sekt1953/HomeAssistant-NSPanel/First_Try/Nextion/Image/0.png

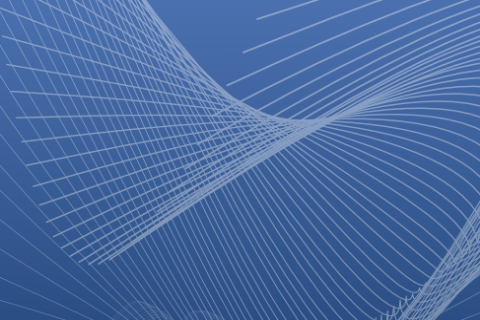
First_Try/Nextion/Image/0.png
