sekt1953/HomeAssistant-NSPanel/NewPageLayout/FreeCad/images/Ver.002/Skærmbillede fra 2022-05-21 14-03-34.png

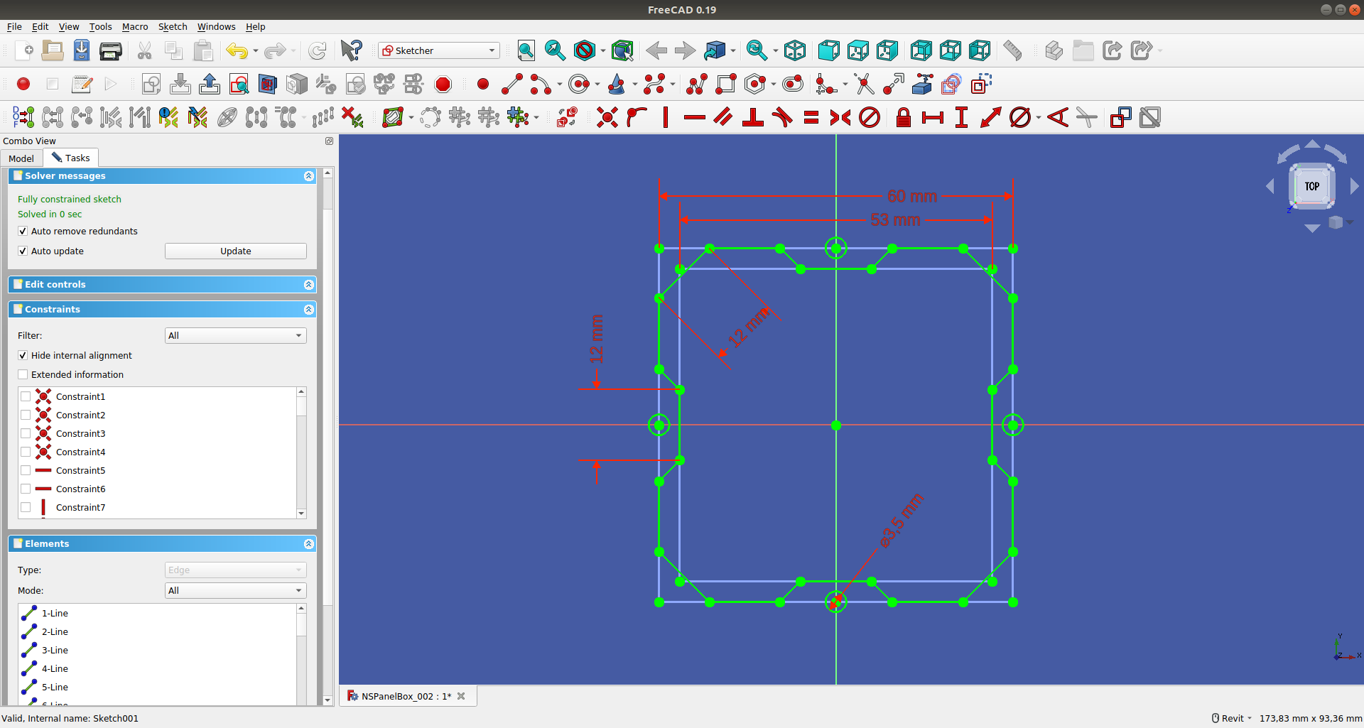
NewPageLayout/FreeCad/images/Ver.002/Skærmbillede fra 2022-05-21 14-03-34.png
