sekt1953/HomeAssistant-NSPanel/NewPageLayout/FreeCad/images/Ver.002/Skærmbillede fra 2022-05-21 14-05-45.png

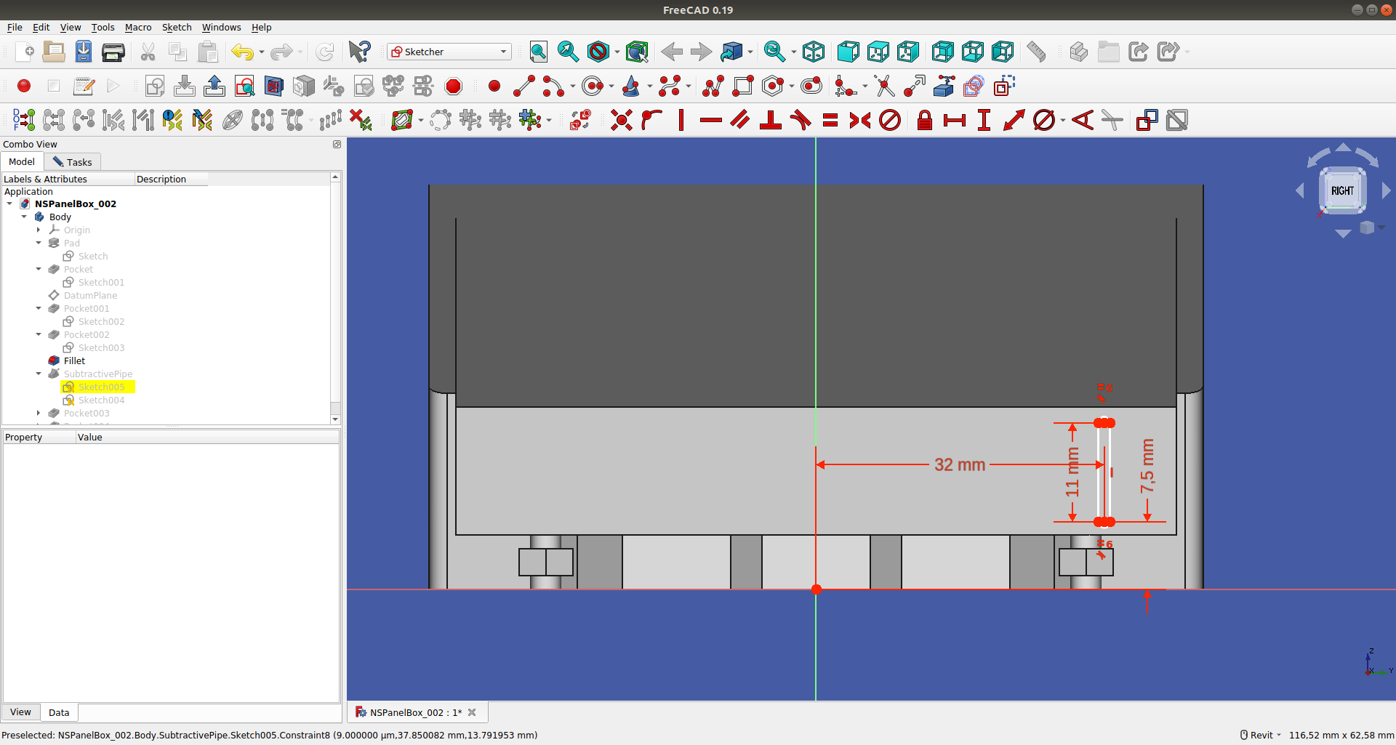
NewPageLayout/FreeCad/images/Ver.002/Skærmbillede fra 2022-05-21 14-05-45.png
