sekt1953/HomeAssistant-NSPanel/NewPageLayout/png/Background.png

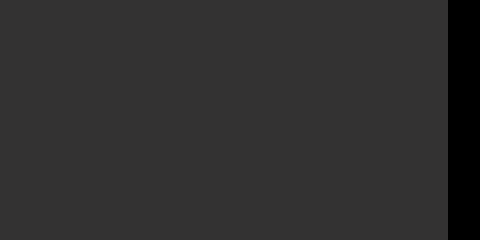
NewPageLayout/png/Background.png
