sekt1953/HomeAssistant-NSPanel/NewPageLayout/png/QuickPage.png

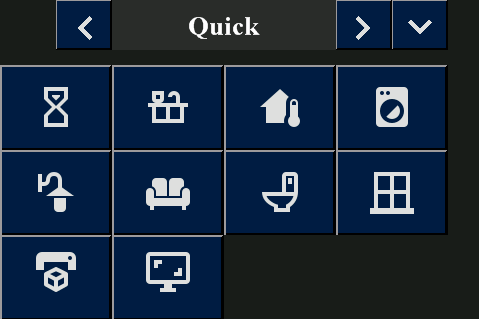
NewPageLayout/png/QuickPage.png
